goldenpixelcompany/La-lumi-re-tous-les-tages-ERROR441/SEND PIX/montageENSADLED1.jpg

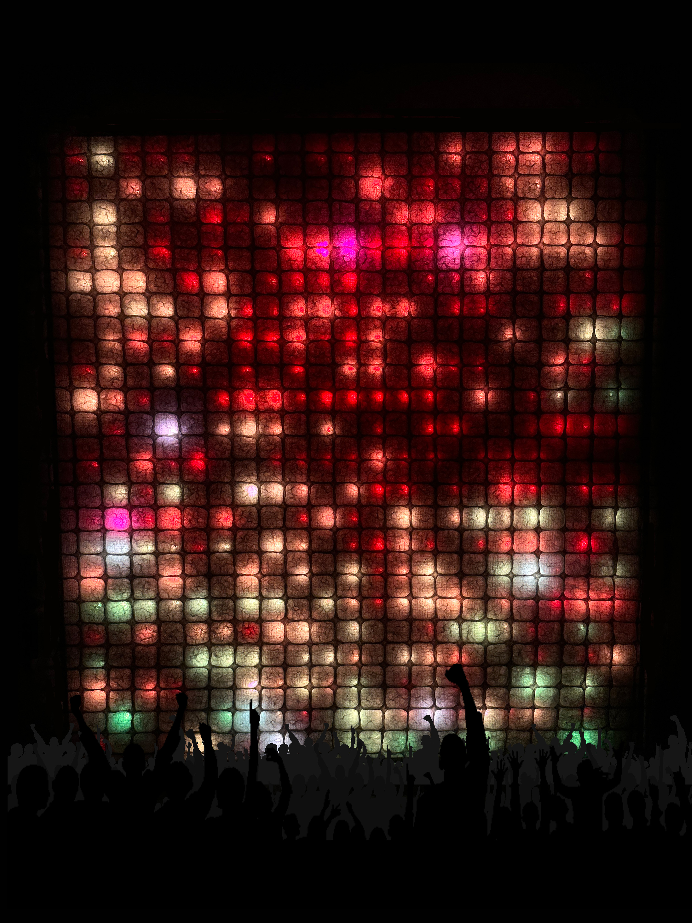
SEND PIX/montageENSADLED1.jpg
