goldenpixelcompany/La-lumi-re-tous-les-tages-ERROR441/Links/pcb_blue.jpg

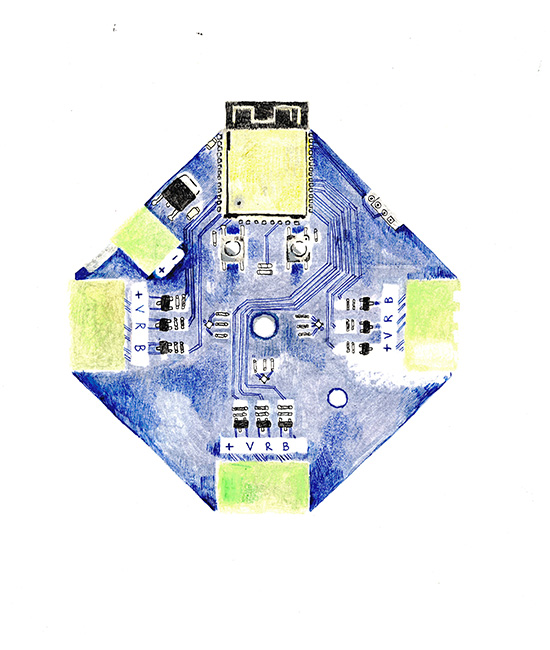
Links/pcb_blue.jpg
