goldenpixelcompany/La-lumi-re-tous-les-tages-ERROR441/Links/1x/Plan de travail 1.png

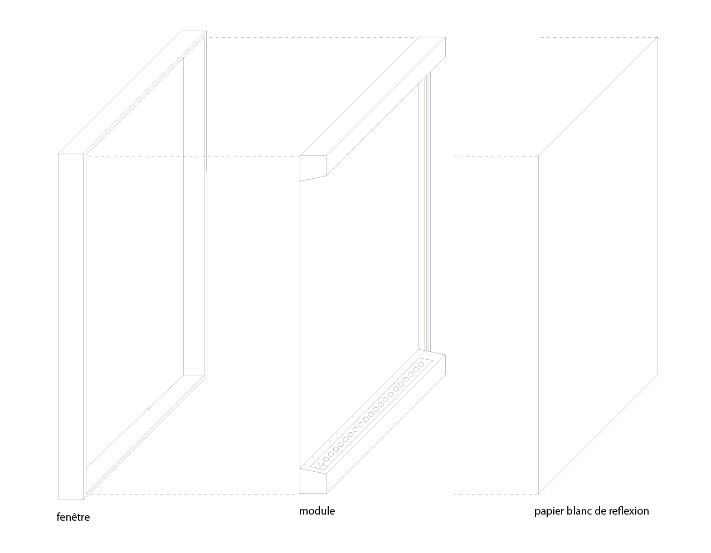
Links/1x/Plan de travail 1.png
