goldenpixelcompany/La-lumi-re-tous-les-tages-ERROR441/Links/enorme-metapixel.jpg

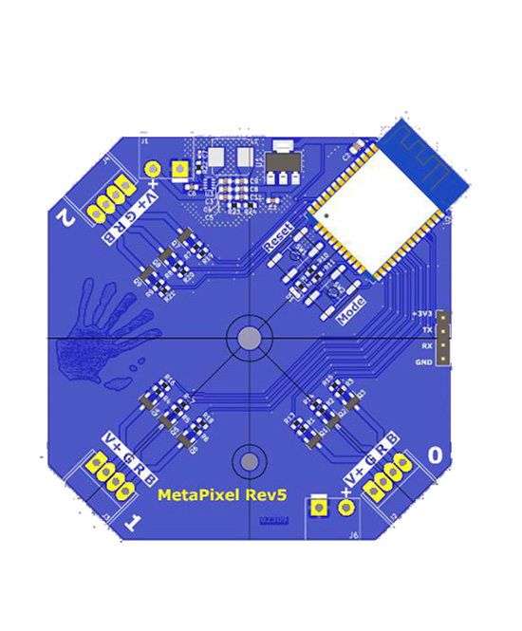
Links/enorme-metapixel.jpg
