goldenpixelcompany/La-lumi-re-tous-les-tages-ERROR441/Links/facade01.png

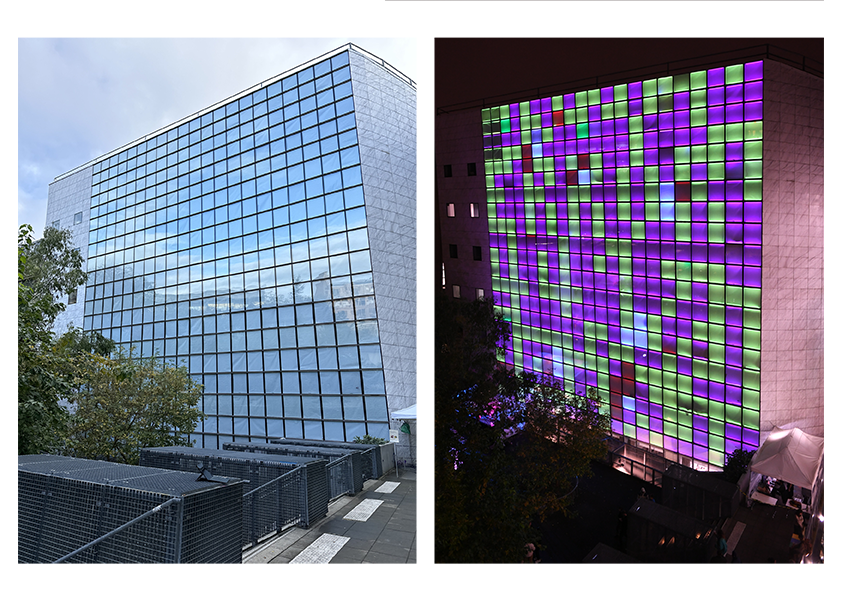
Links/facade01.png
