goldenpixelcompany/La-lumi-re-tous-les-tages-ERROR441/Links/pcb01.jpg

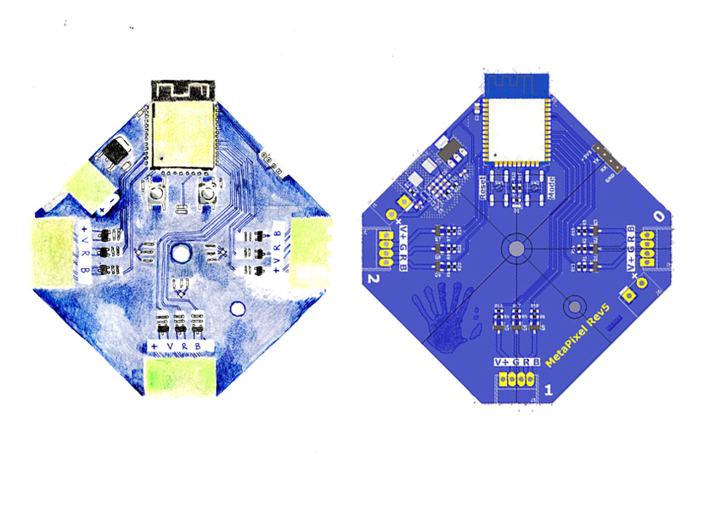
Links/pcb01.jpg
