goldenpixelcompany/La-lumi-re-tous-les-tages-ERROR441/metapixel_hardware/bluehand_BW.png

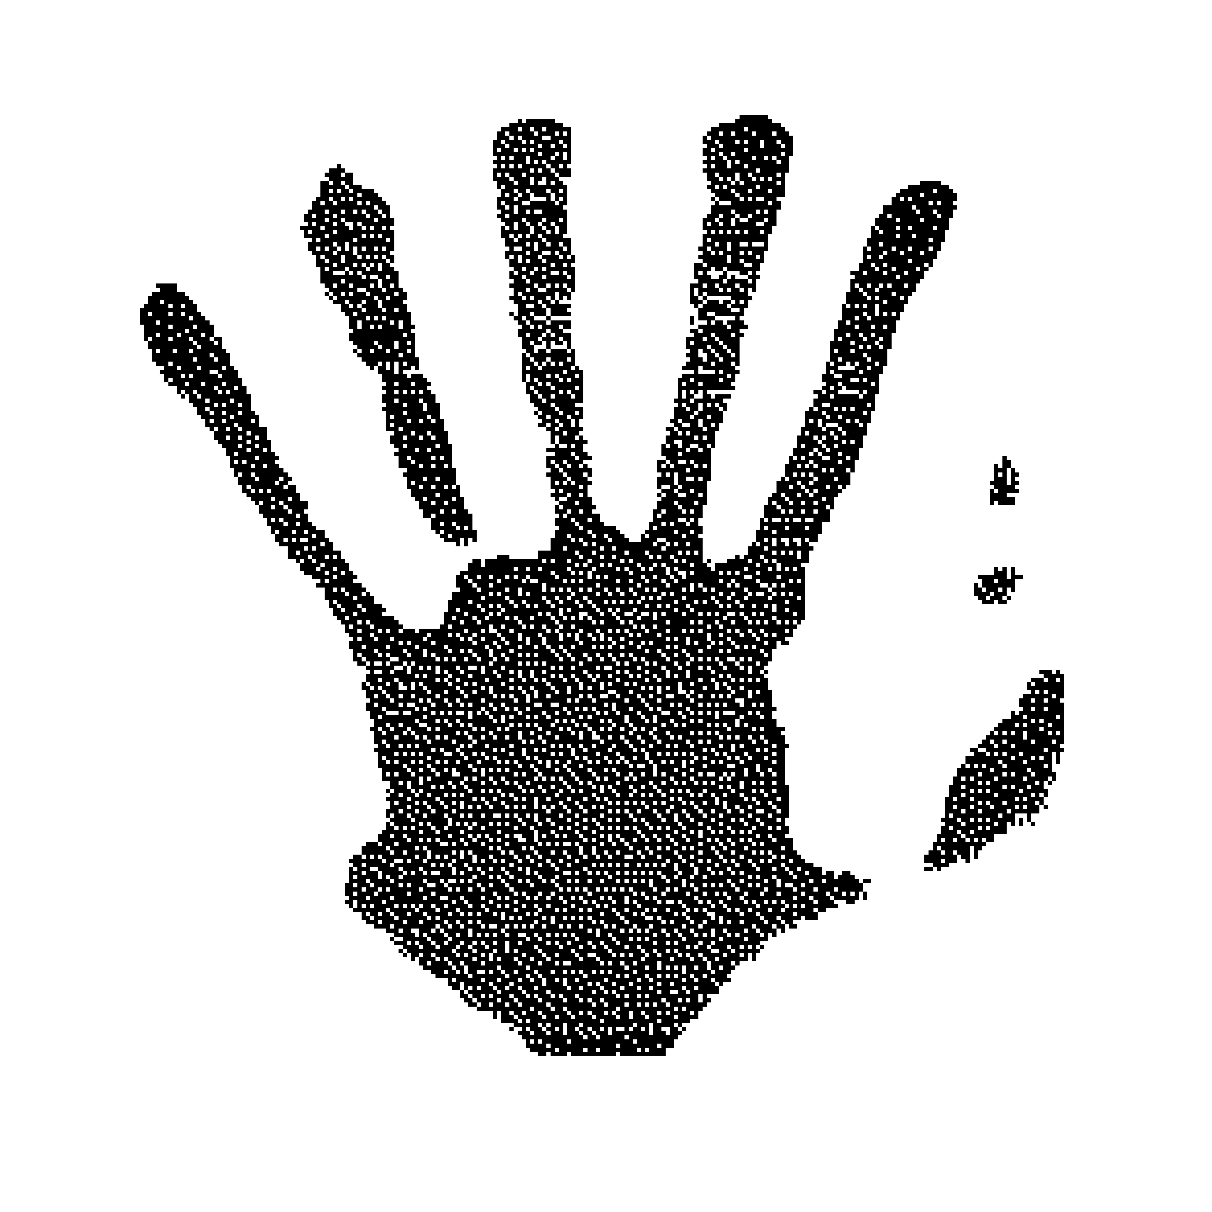
metapixel_hardware/bluehand_BW.png
