goldenpixelcompany/La-lumi-re-tous-les-tages-ERROR441/SEND PIX/affiche.png

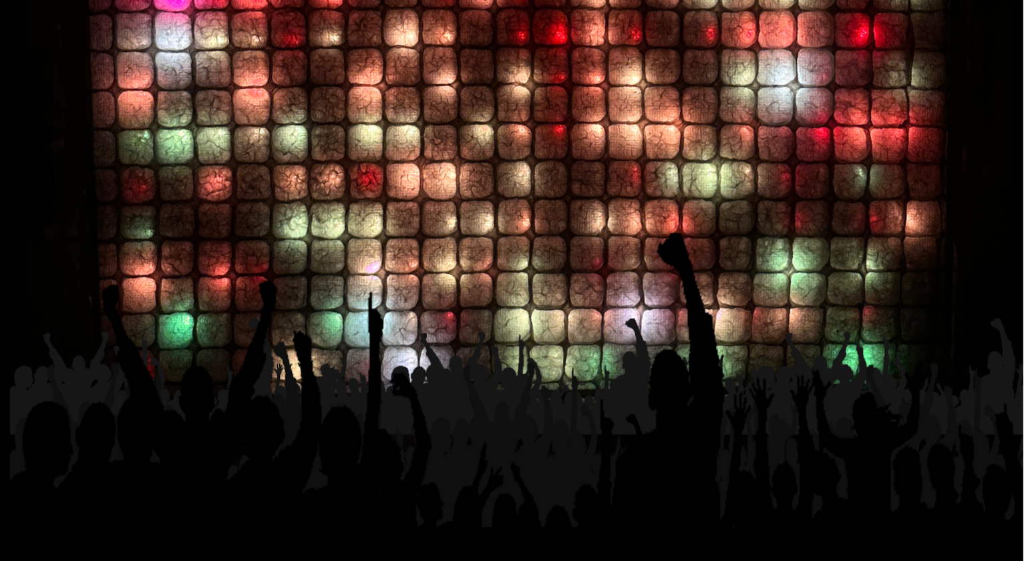
SEND PIX/affiche.png
